MKme/EduCase-Portable-Classroom/Images/6289021474756650785.PNG

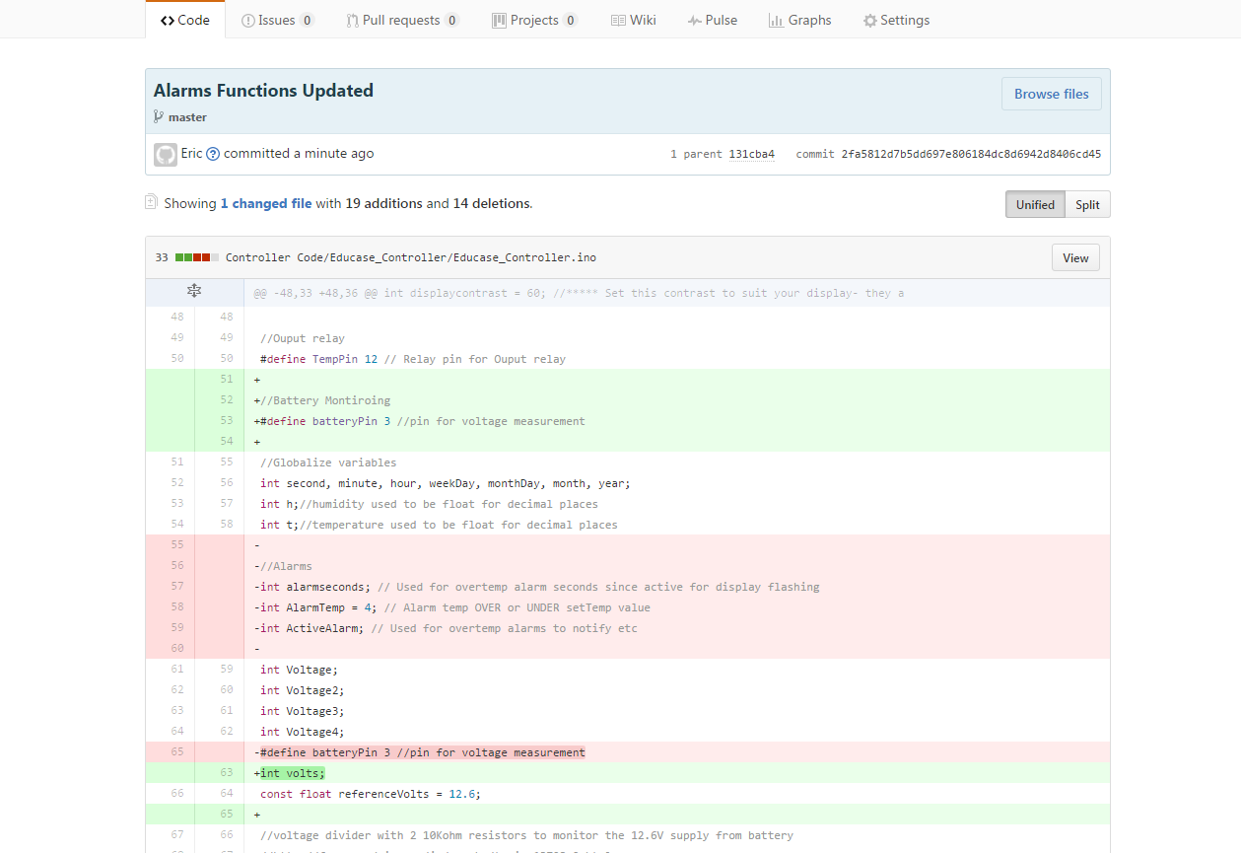
Images/6289021474756650785.PNG
