MKme/EduCase-Portable-Classroom/Images/ArduinoContent.PNG

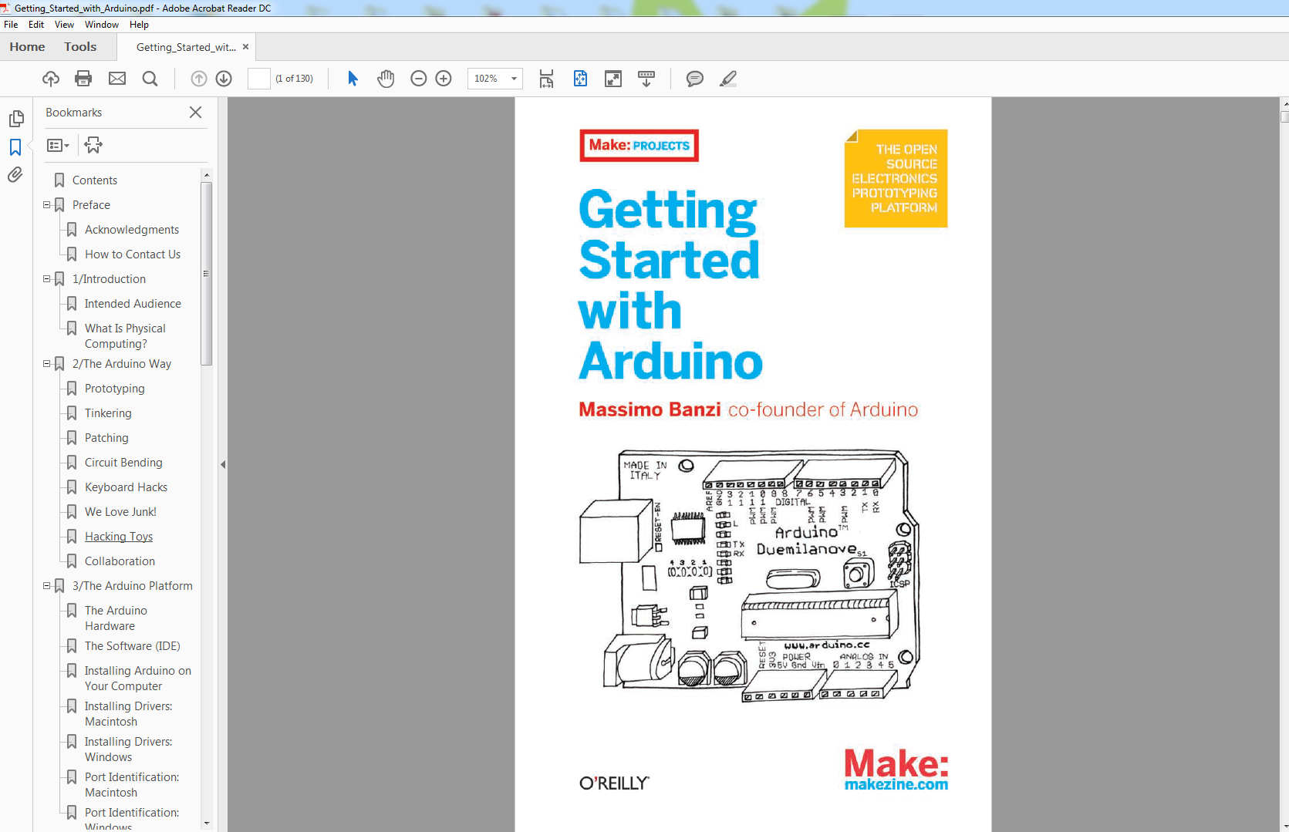
Images/ArduinoContent.PNG
