MKme/EduCase-Portable-Classroom/Images/L band .PNG

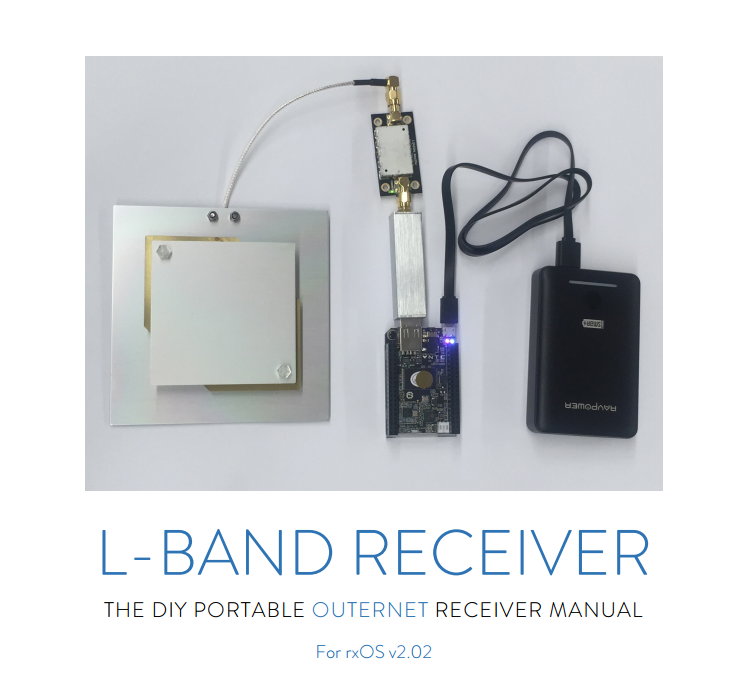
Images/L band .PNG
