MKme/EduCase-Portable-Classroom/Images/pelicancases.PNG

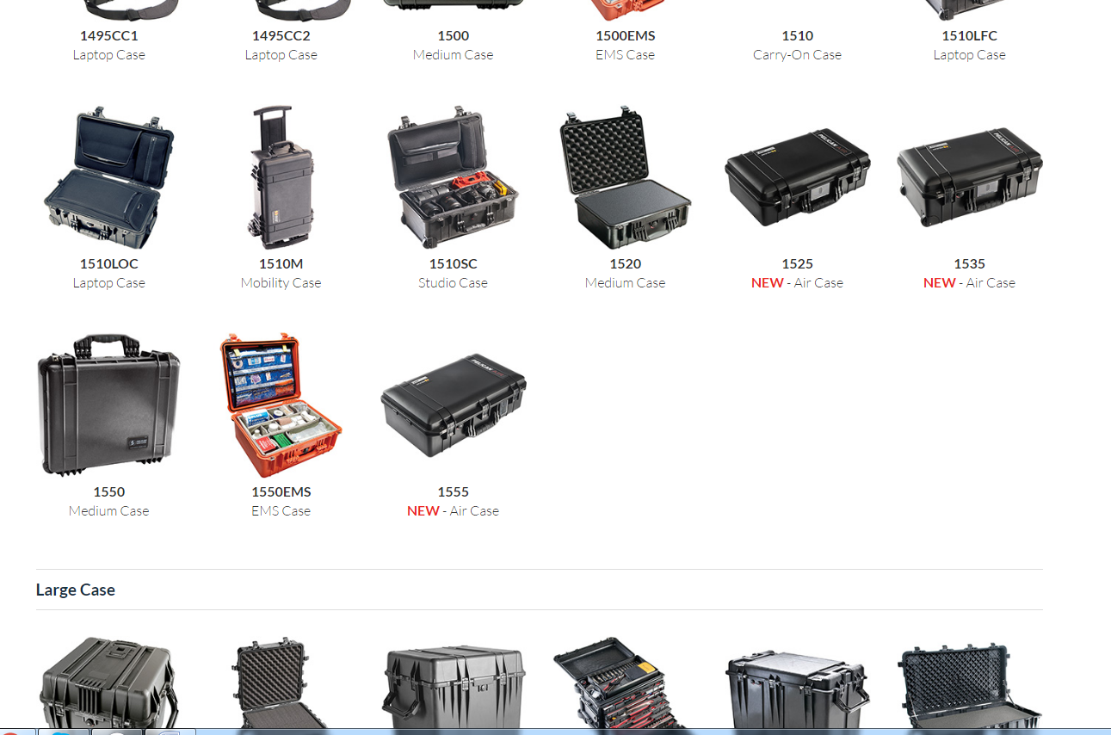
Images/pelicancases.PNG
