MKme/EduCase-Portable-Classroom/Images/school.jpg

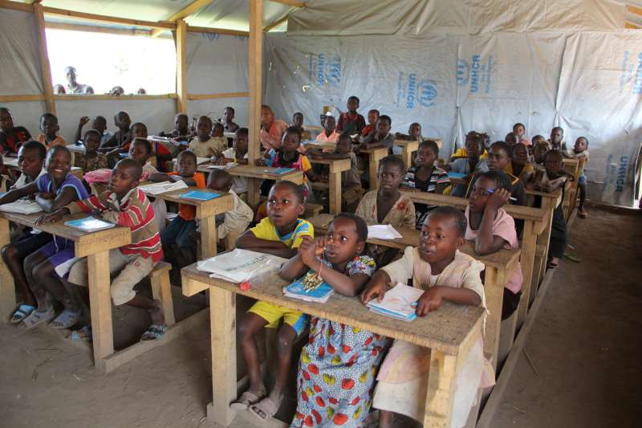
Images/school.jpg
