MKme/EduCase-Portable-Classroom/Images/SDD2.PNG

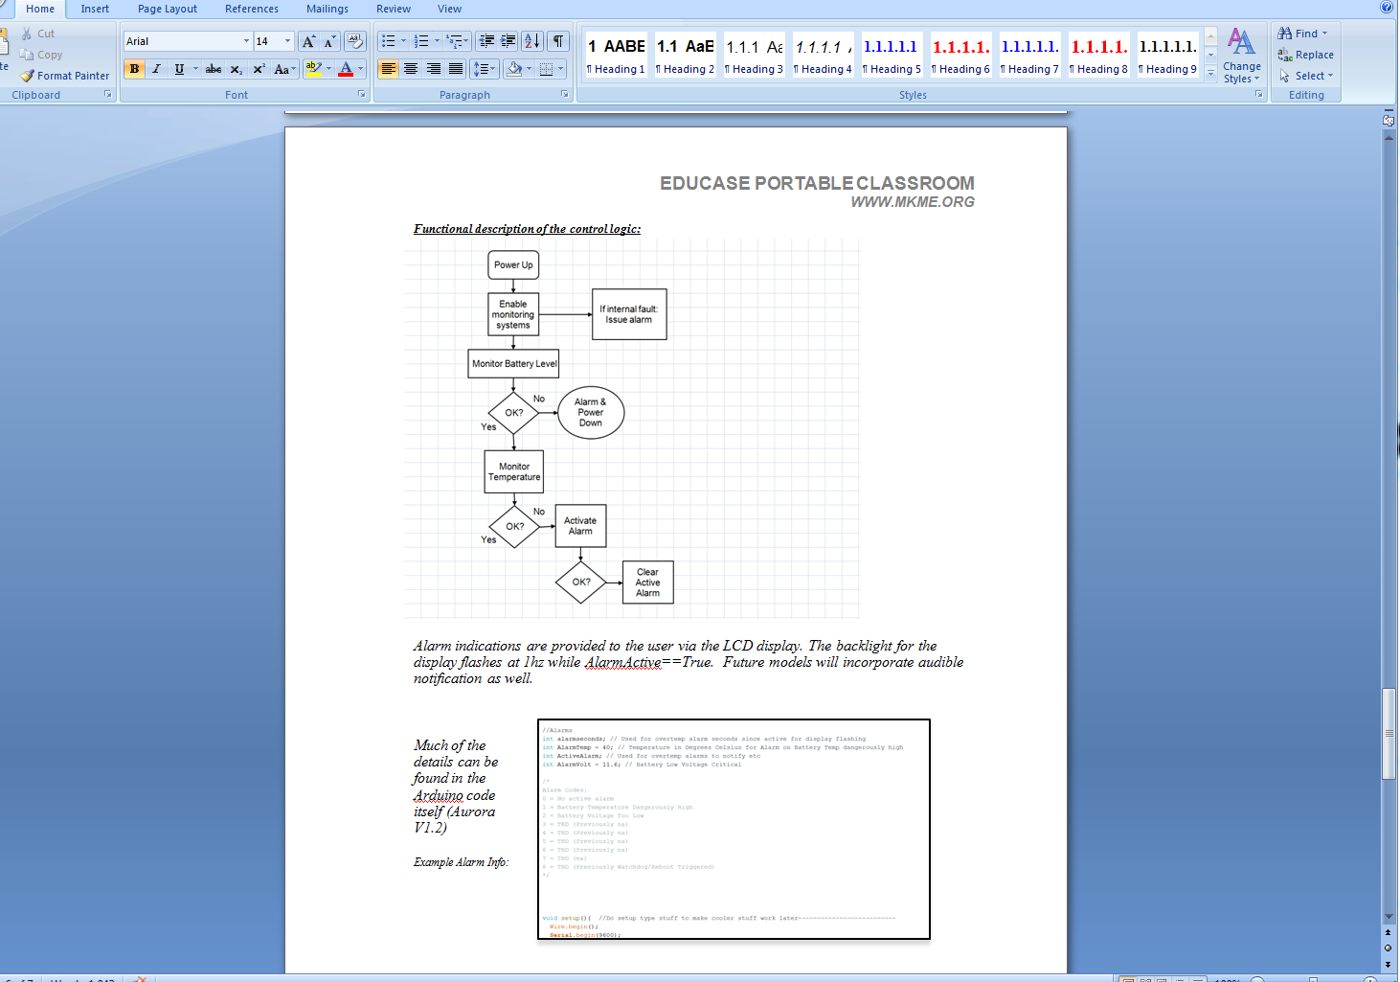
Images/SDD2.PNG
