MKme/EduCase-Portable-Classroom/Images/SDD Update.PNG

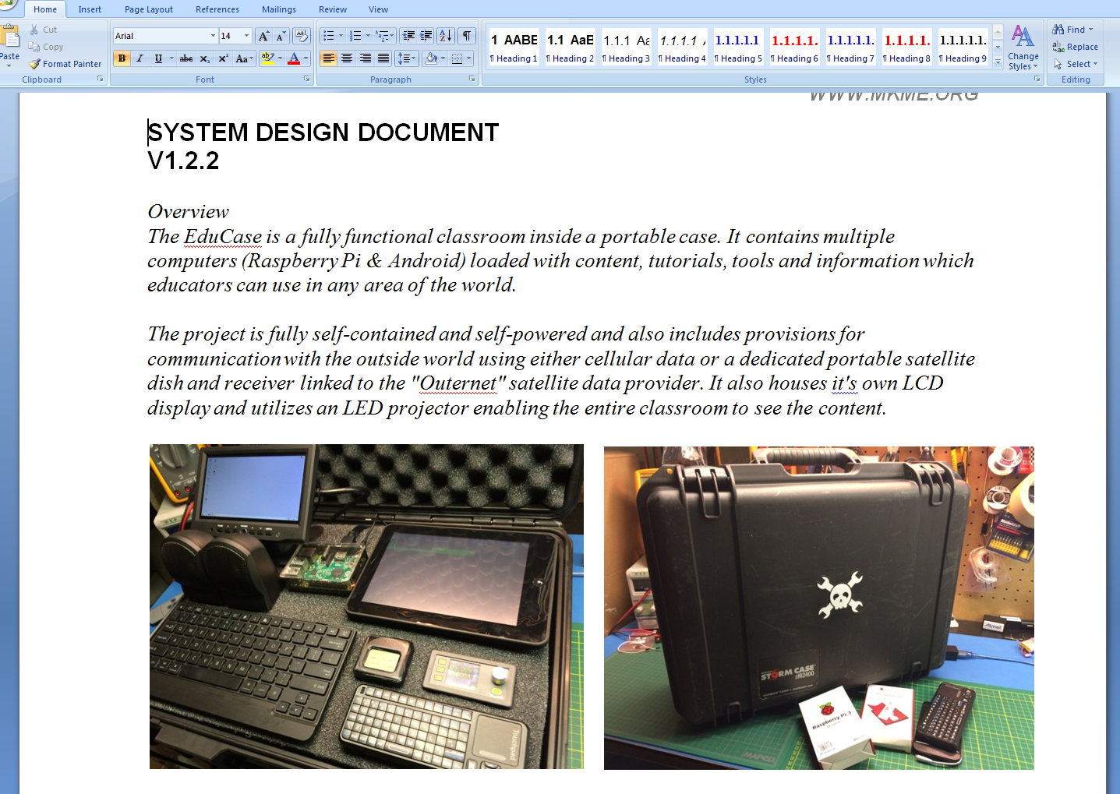
Images/SDD Update.PNG
