MKme/EduCase-Portable-Classroom/Images/Assem,bly Guide.PNG

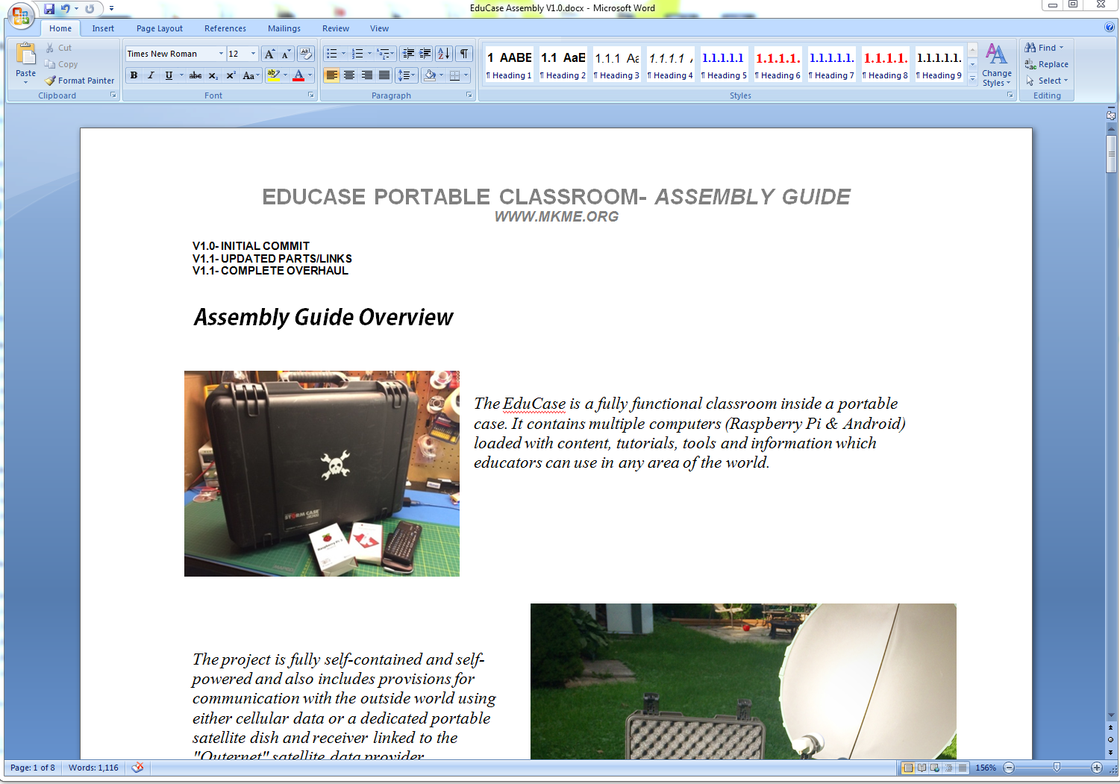
Images/Assem,bly Guide.PNG
