MKme/EduCase-Portable-Classroom/Images/Assembly2.PNG

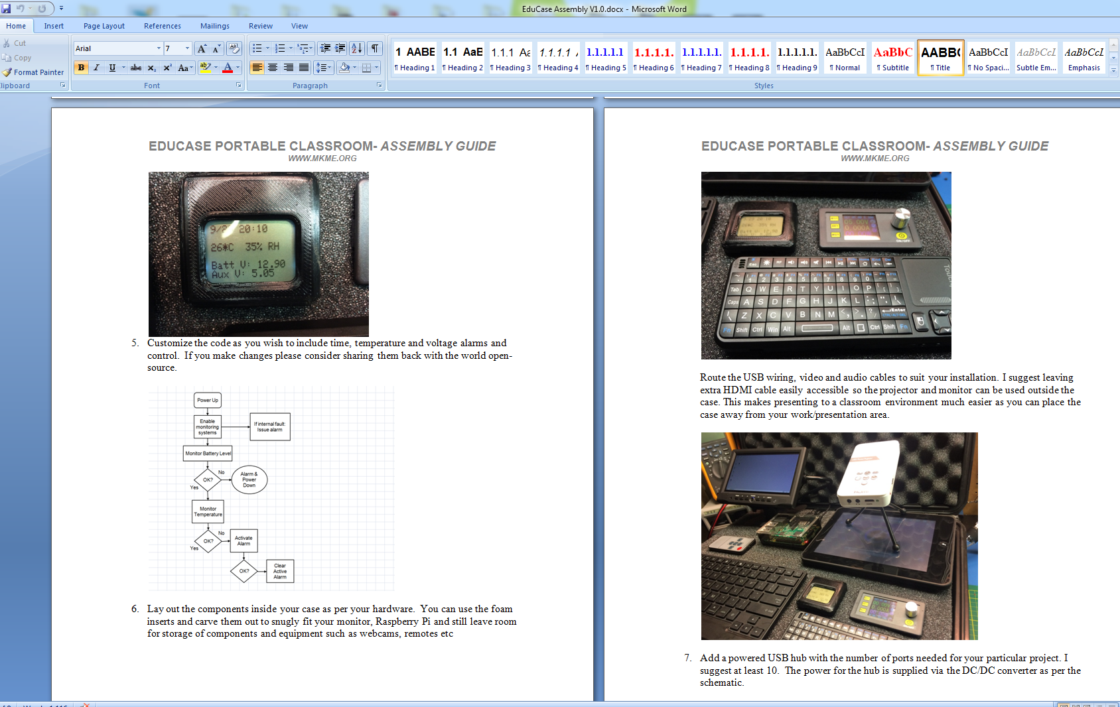
Images/Assembly2.PNG
