MKme/EduCase-Portable-Classroom/Images/Portable Dish Setup.jpg

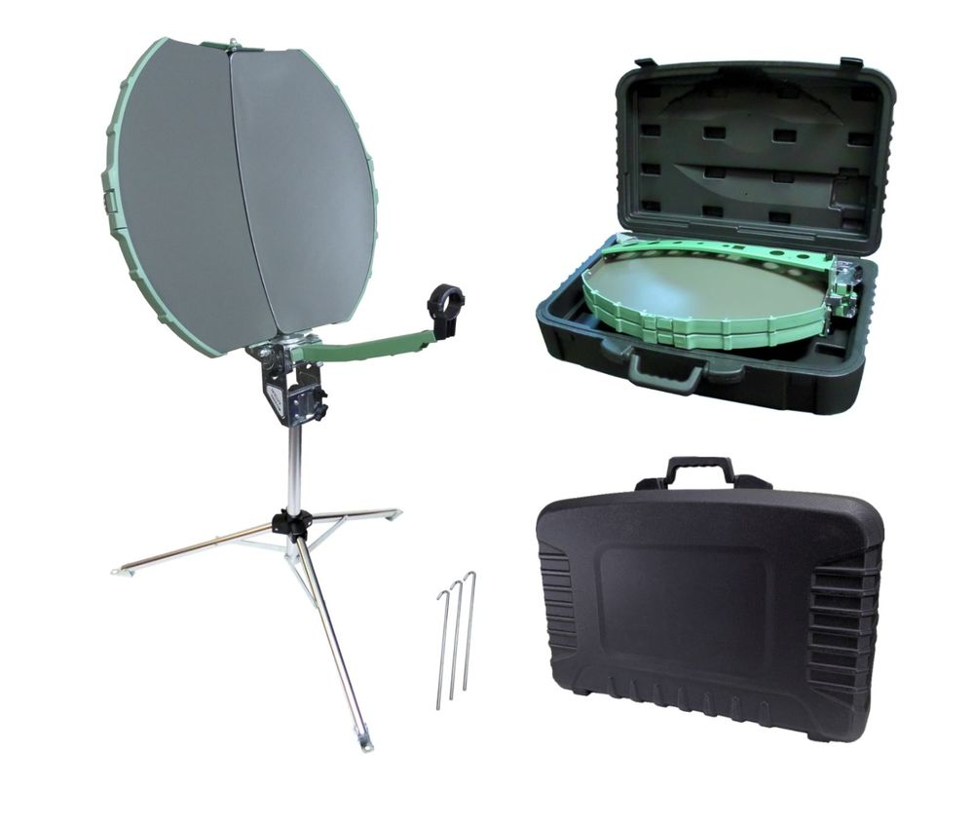
Images/Portable Dish Setup.jpg
